jshendriks/MATHerials-internship/Results/Preliminary prototypes/WeightsPrototype1.jpeg

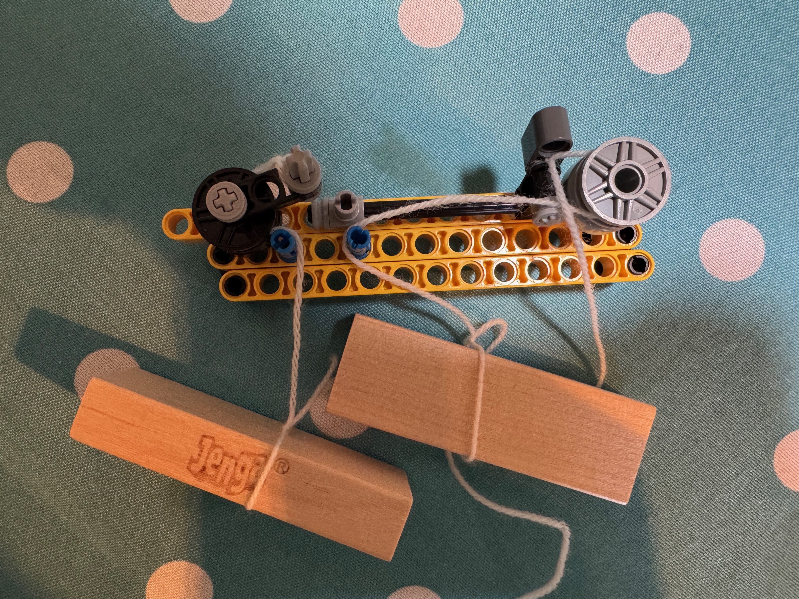
Results/Preliminary prototypes/WeightsPrototype1.jpeg
