jshendriks/MATHerials-internship/Results/User/Gebruiker2.png

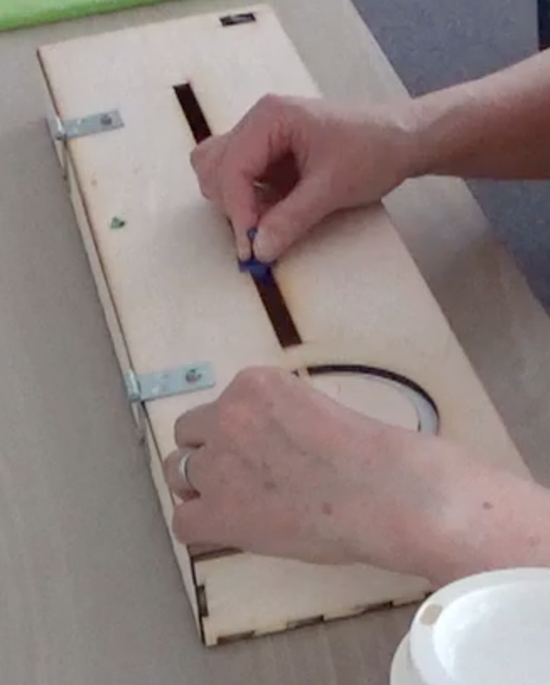
Results/User/Gebruiker2.png
