jshendriks/MATHerials-internship/Results/Appearance/BinnenKant1.jpeg

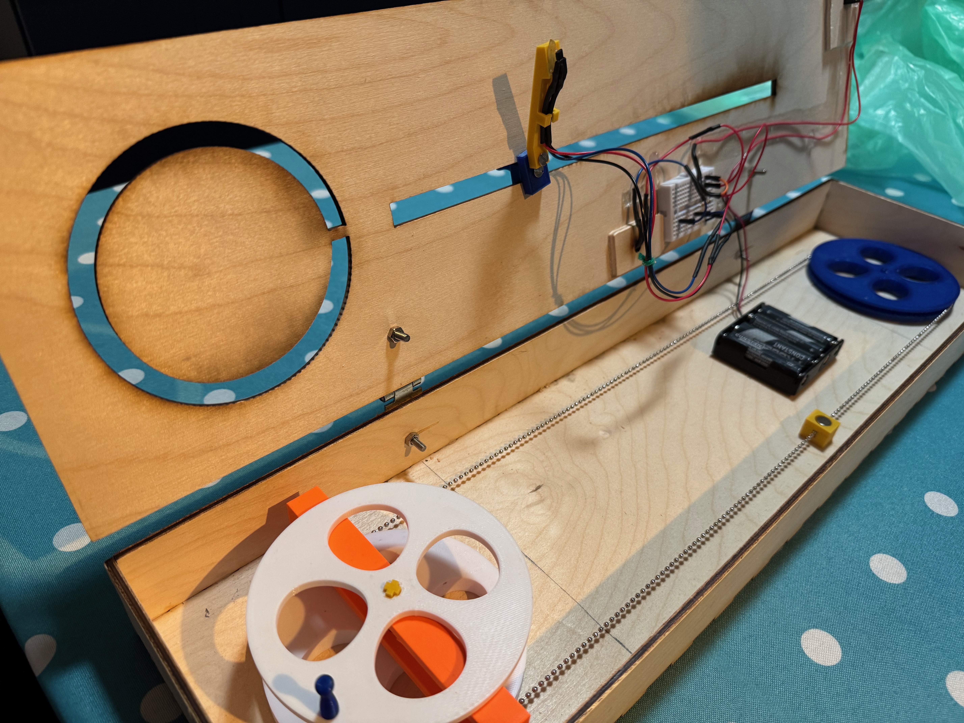
Results/Appearance/BinnenKant1.jpeg
