jshendriks/MATHerials-internship/Results/Appearance/BinnenKant2.jpeg

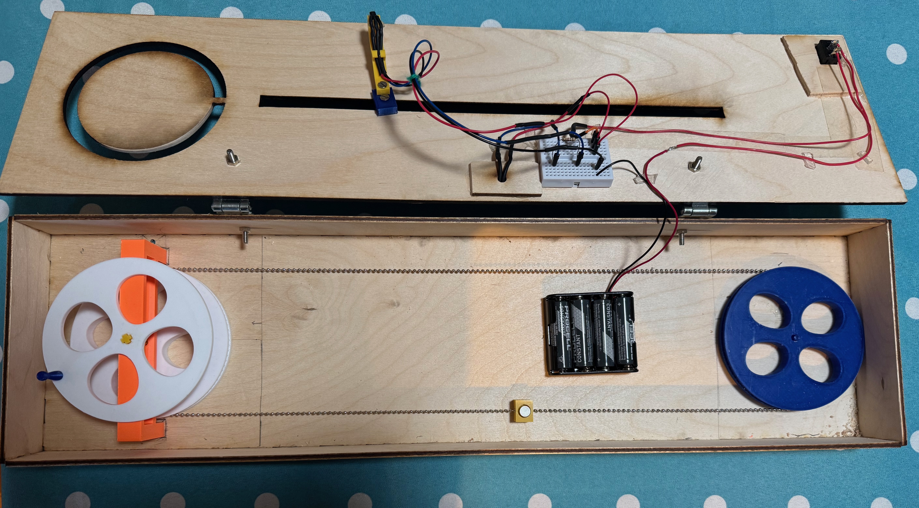
Results/Appearance/BinnenKant2.jpeg
