jshendriks/MATHerials-internship/Results/Appearance/ZijAanzicht.jpeg

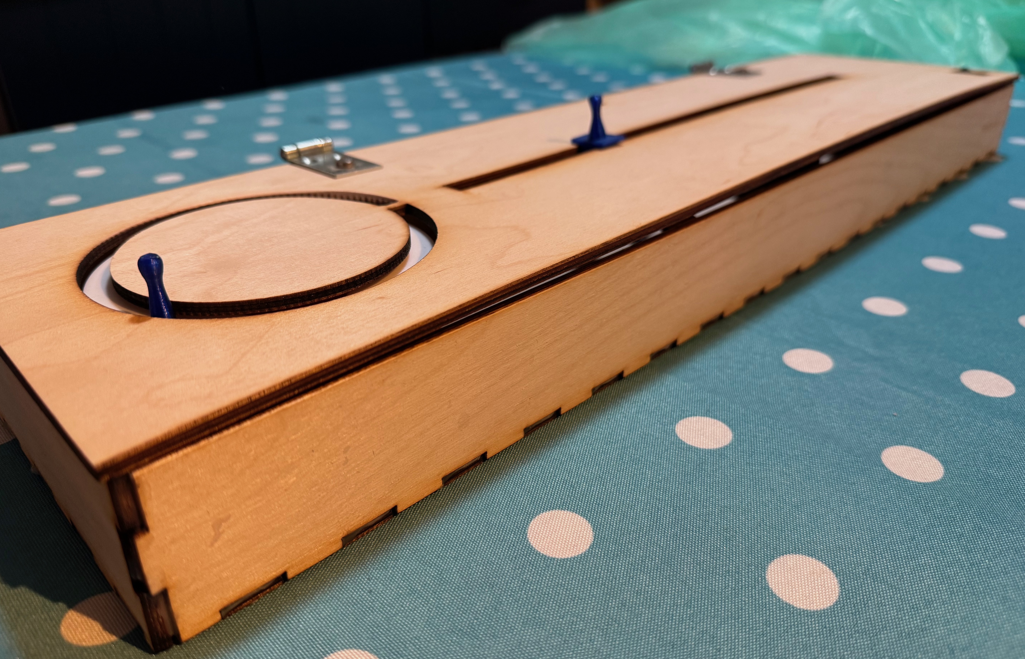
Results/Appearance/ZijAanzicht.jpeg
