jshendriks/MATHerials-internship/Results/Preliminary prototypes/GearPrototype1.jpeg

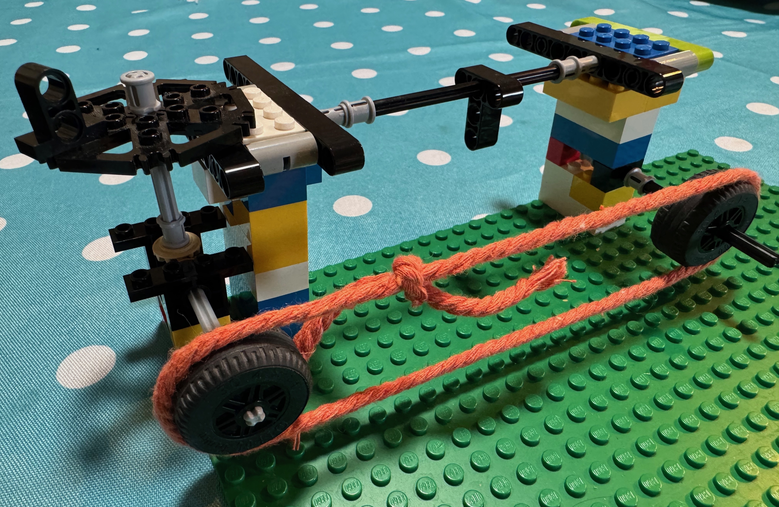
Results/Preliminary prototypes/GearPrototype1.jpeg
