jshendriks/MATHerials-internship/Results/Preliminary prototypes/GearPrototype2.jpeg

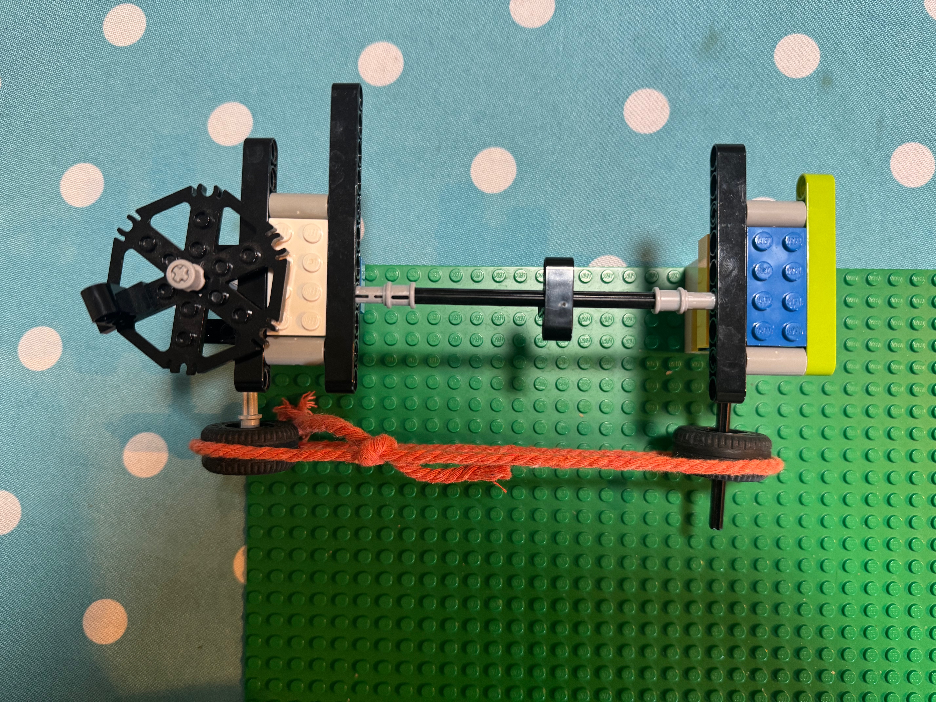
Results/Preliminary prototypes/GearPrototype2.jpeg
