jshendriks/MATHerials-internship/Results/Preliminary prototypes/WeightsPrototype2.jpeg

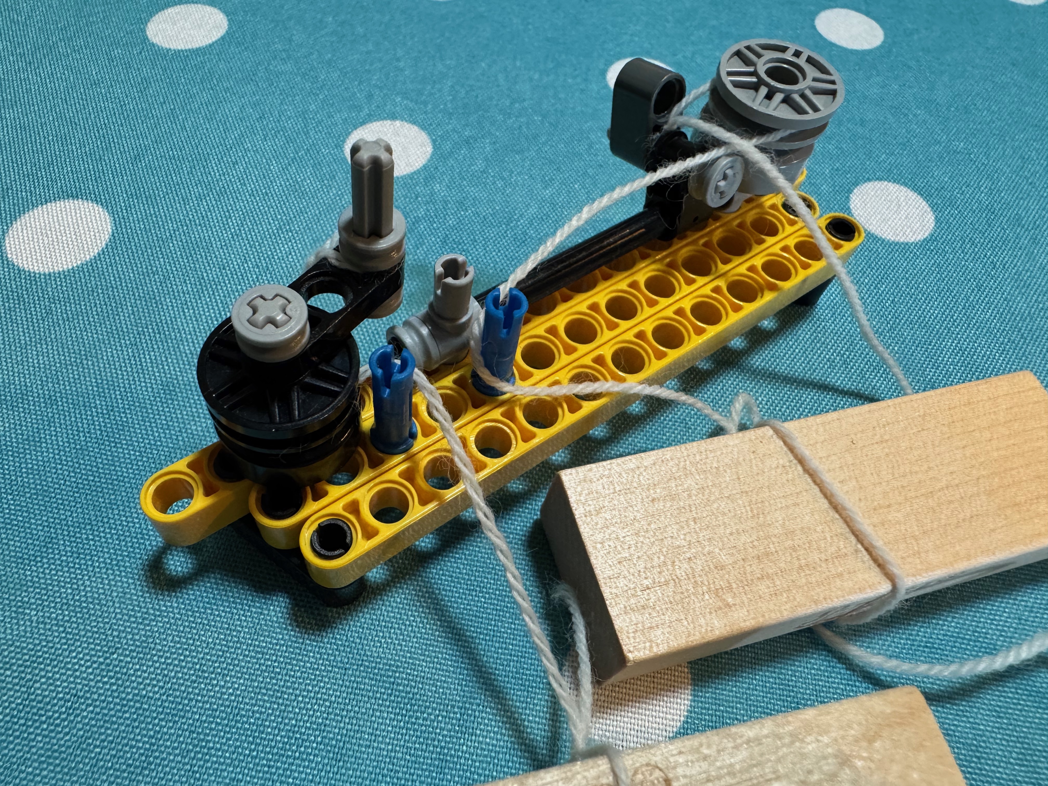
Results/Preliminary prototypes/WeightsPrototype2.jpeg
