jshendriks/MATHerials-internship/Results/User/Gebruiker1.png

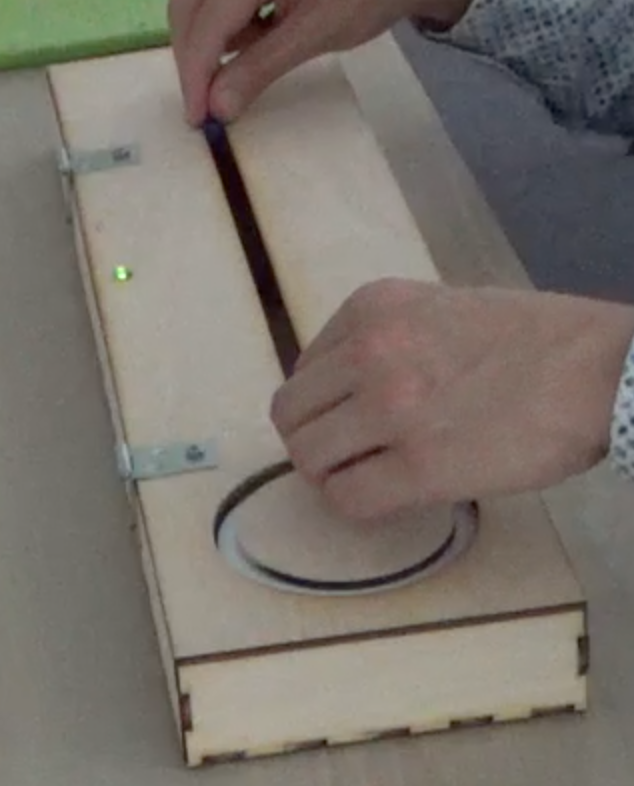
Results/User/Gebruiker1.png
