jshendriks/MATHerials-internship/Results/User/LampjeAan1.jpeg

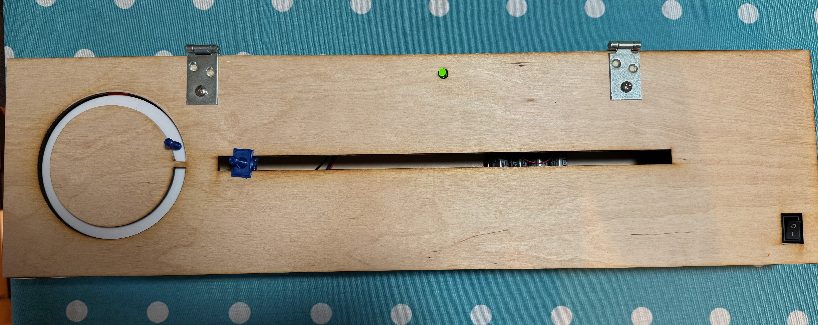
Results/User/LampjeAan1.jpeg
