jshendriks/MATHerials-internship/Results/User/LampjeAan2.jpeg

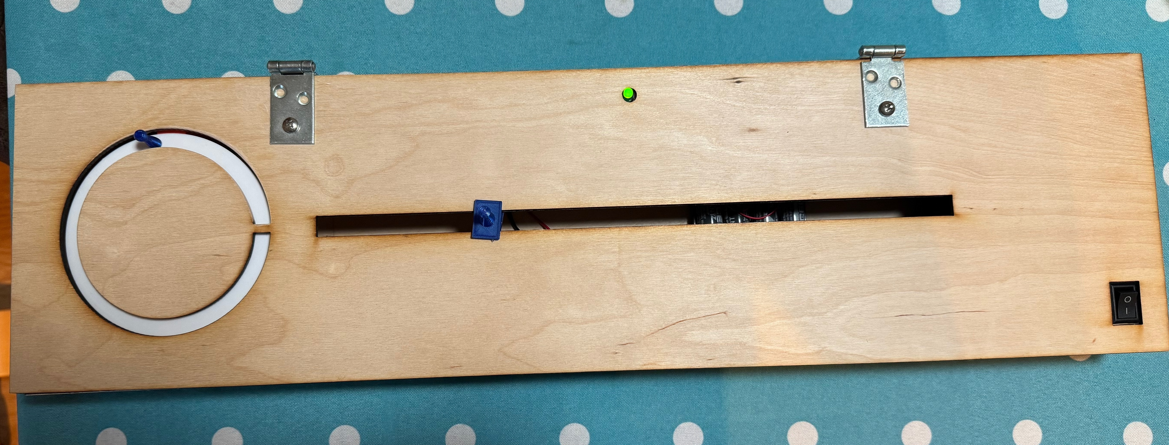
Results/User/LampjeAan2.jpeg
