jshendriks/MATHerials-internship/Results/User/LampjeUit1.jpeg

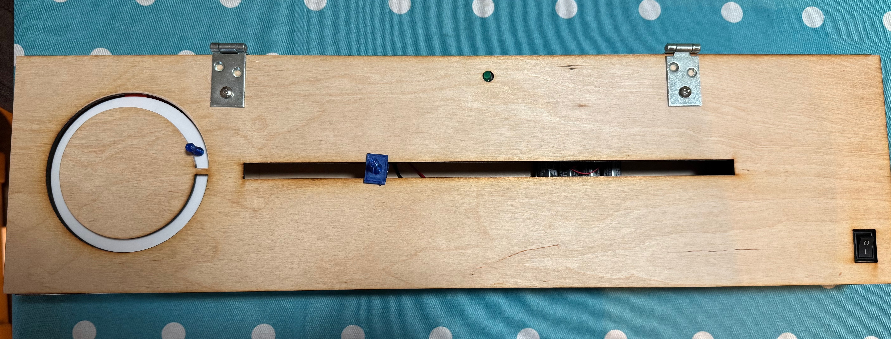
Results/User/LampjeUit1.jpeg
