jshendriks/MATHerials-internship/Results/User/LampjeUit2.jpeg

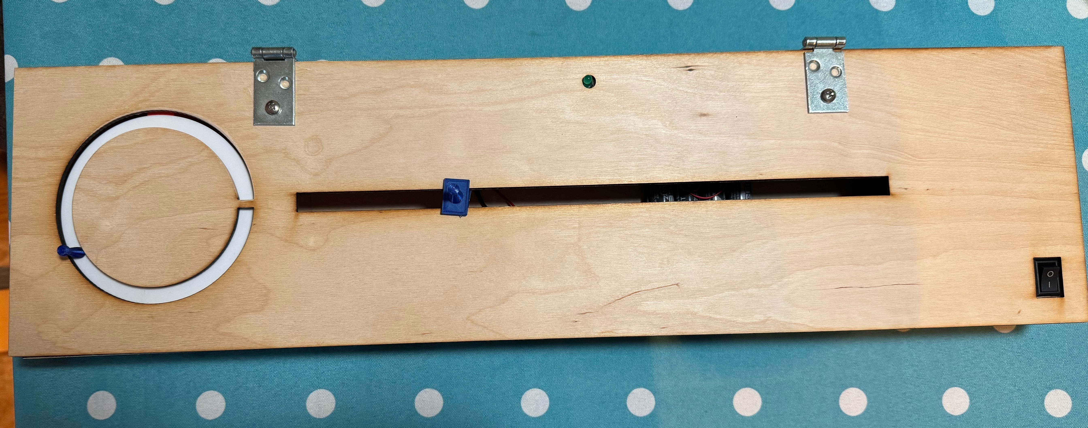
Results/User/LampjeUit2.jpeg
